sullyjason/interactiles/2x2 Interactiles/switch pins.jpg

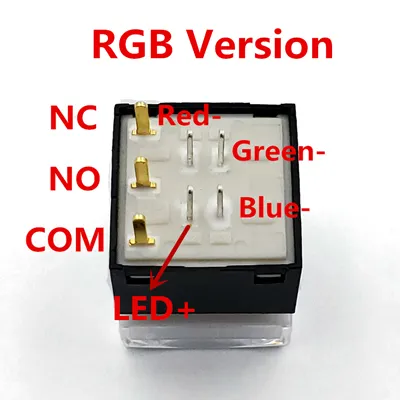
2x2 Interactiles/switch pins.jpg
