sullyjason/interactiles/Interactiles_Controller/Interactiles_Controller.kicad_sch

## KiCad design Interactiles_Controller/Interactiles_Controller.kicad_sch (2026-07-07)

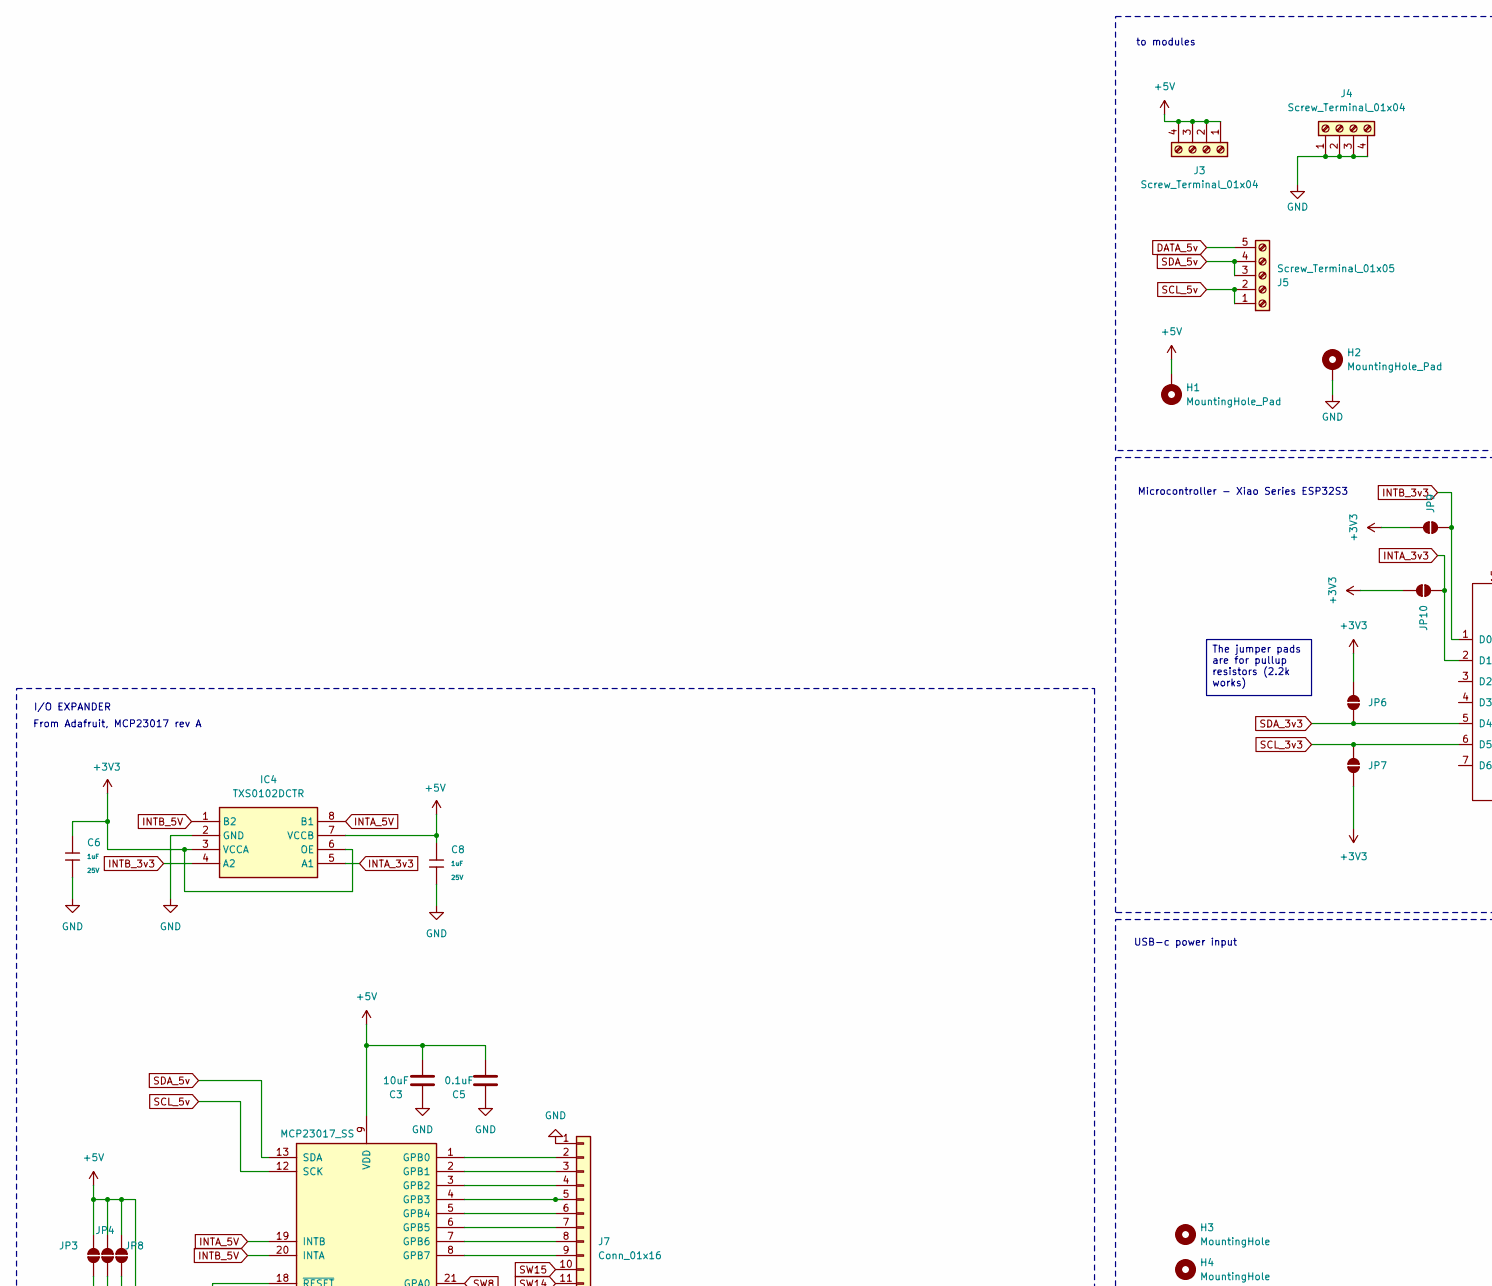
[picture p37: schematic Interactiles_Controller.kicad_sch, part in row 1, column 1]

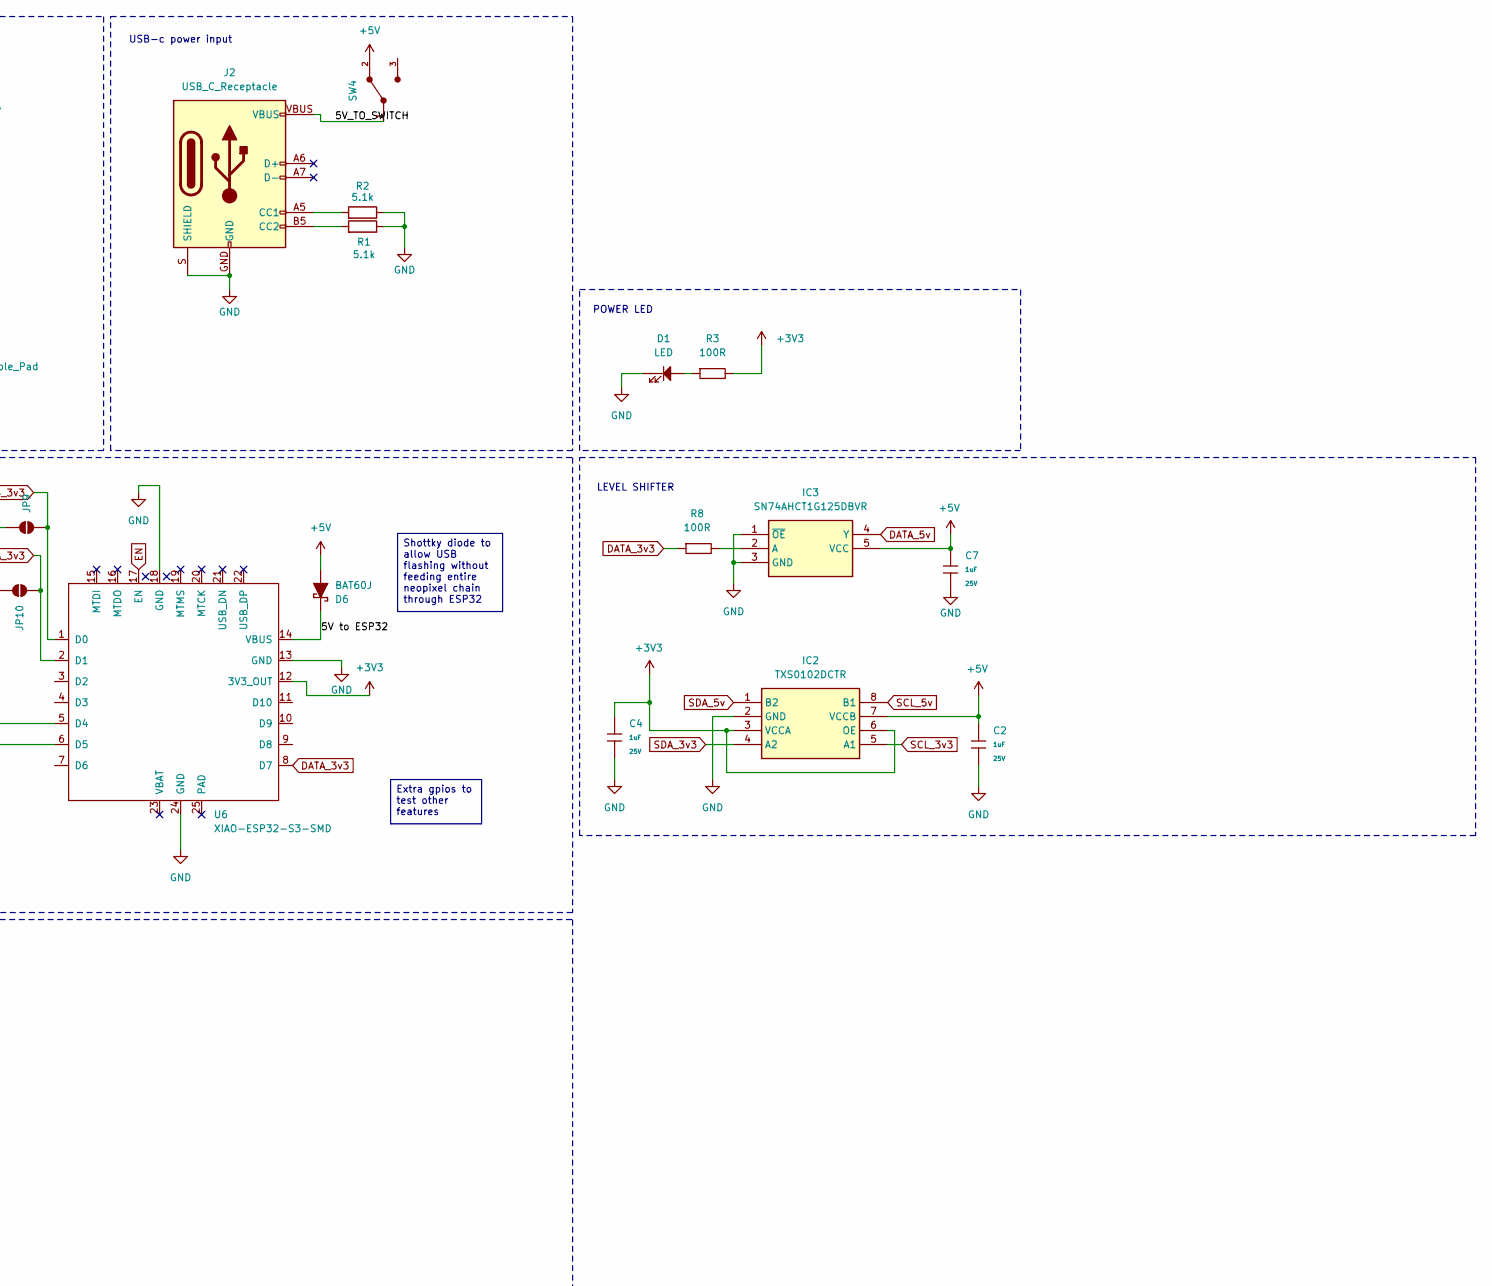
[picture p38: schematic Interactiles_Controller.kicad_sch, part in row 1, column 2]

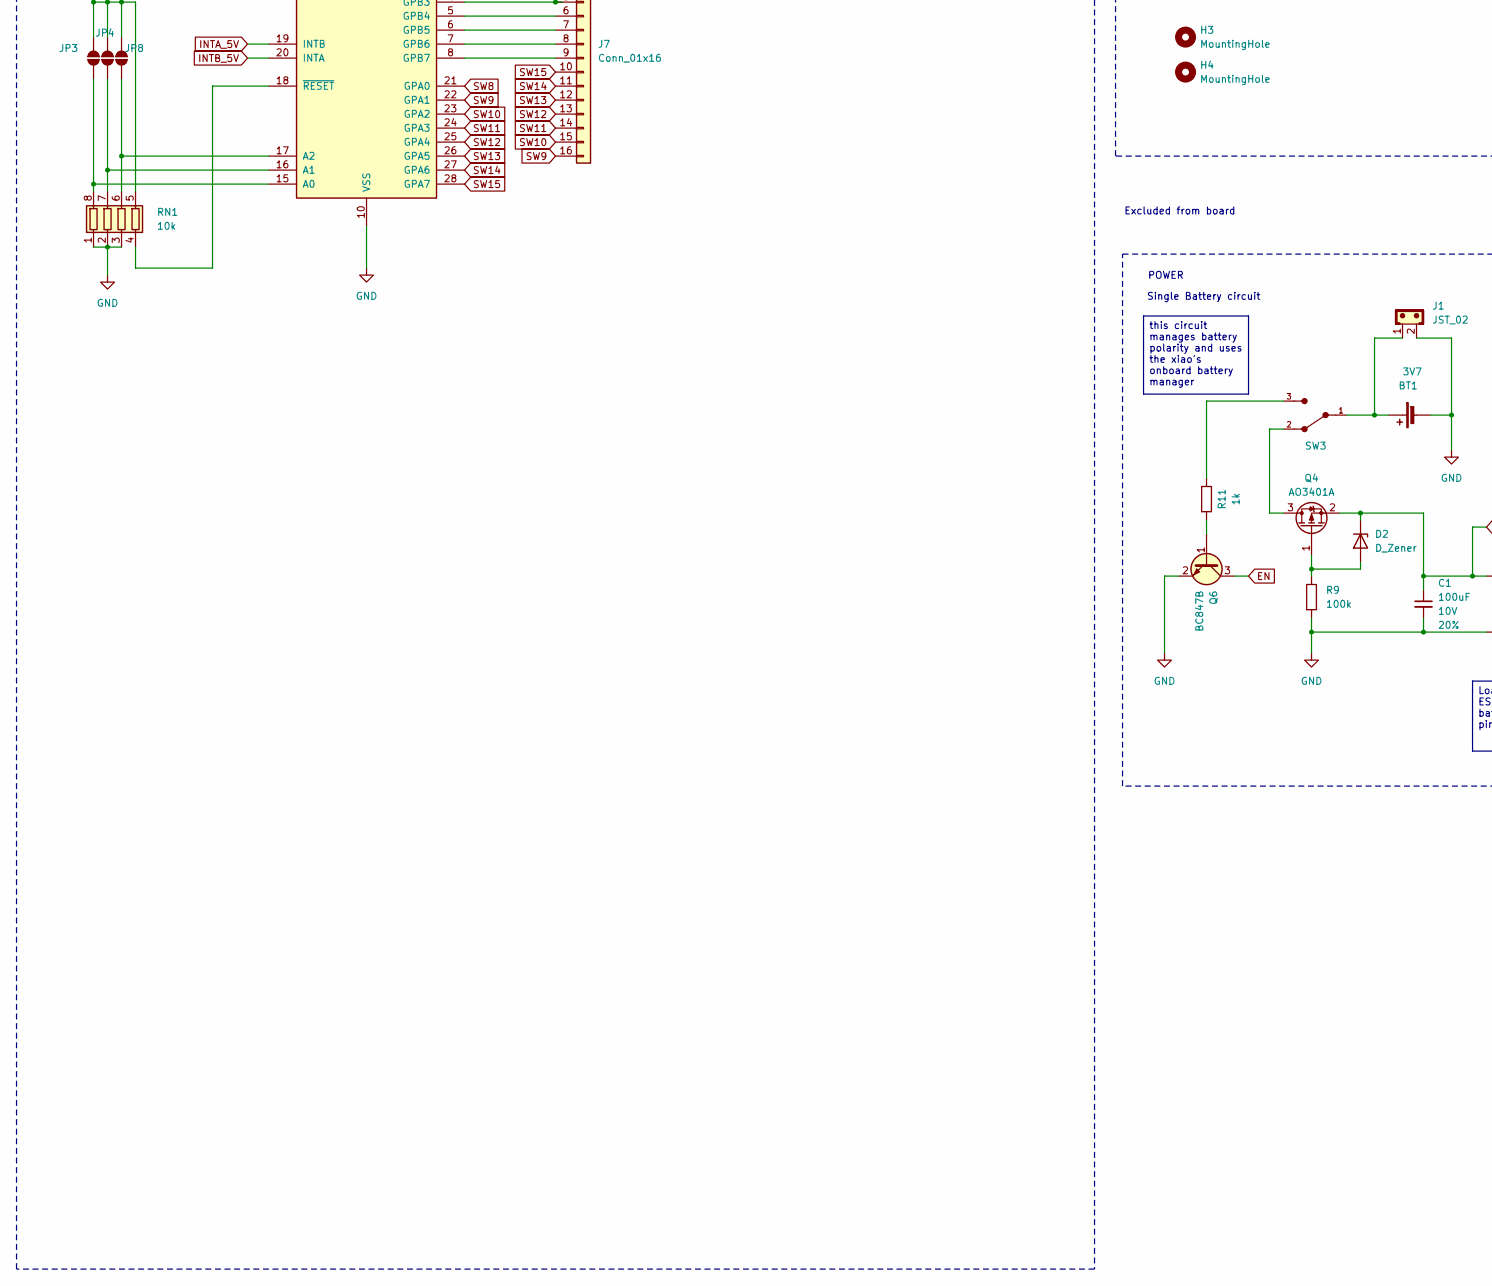
[picture p39: schematic Interactiles_Controller.kicad_sch, part in row 2, column 1]

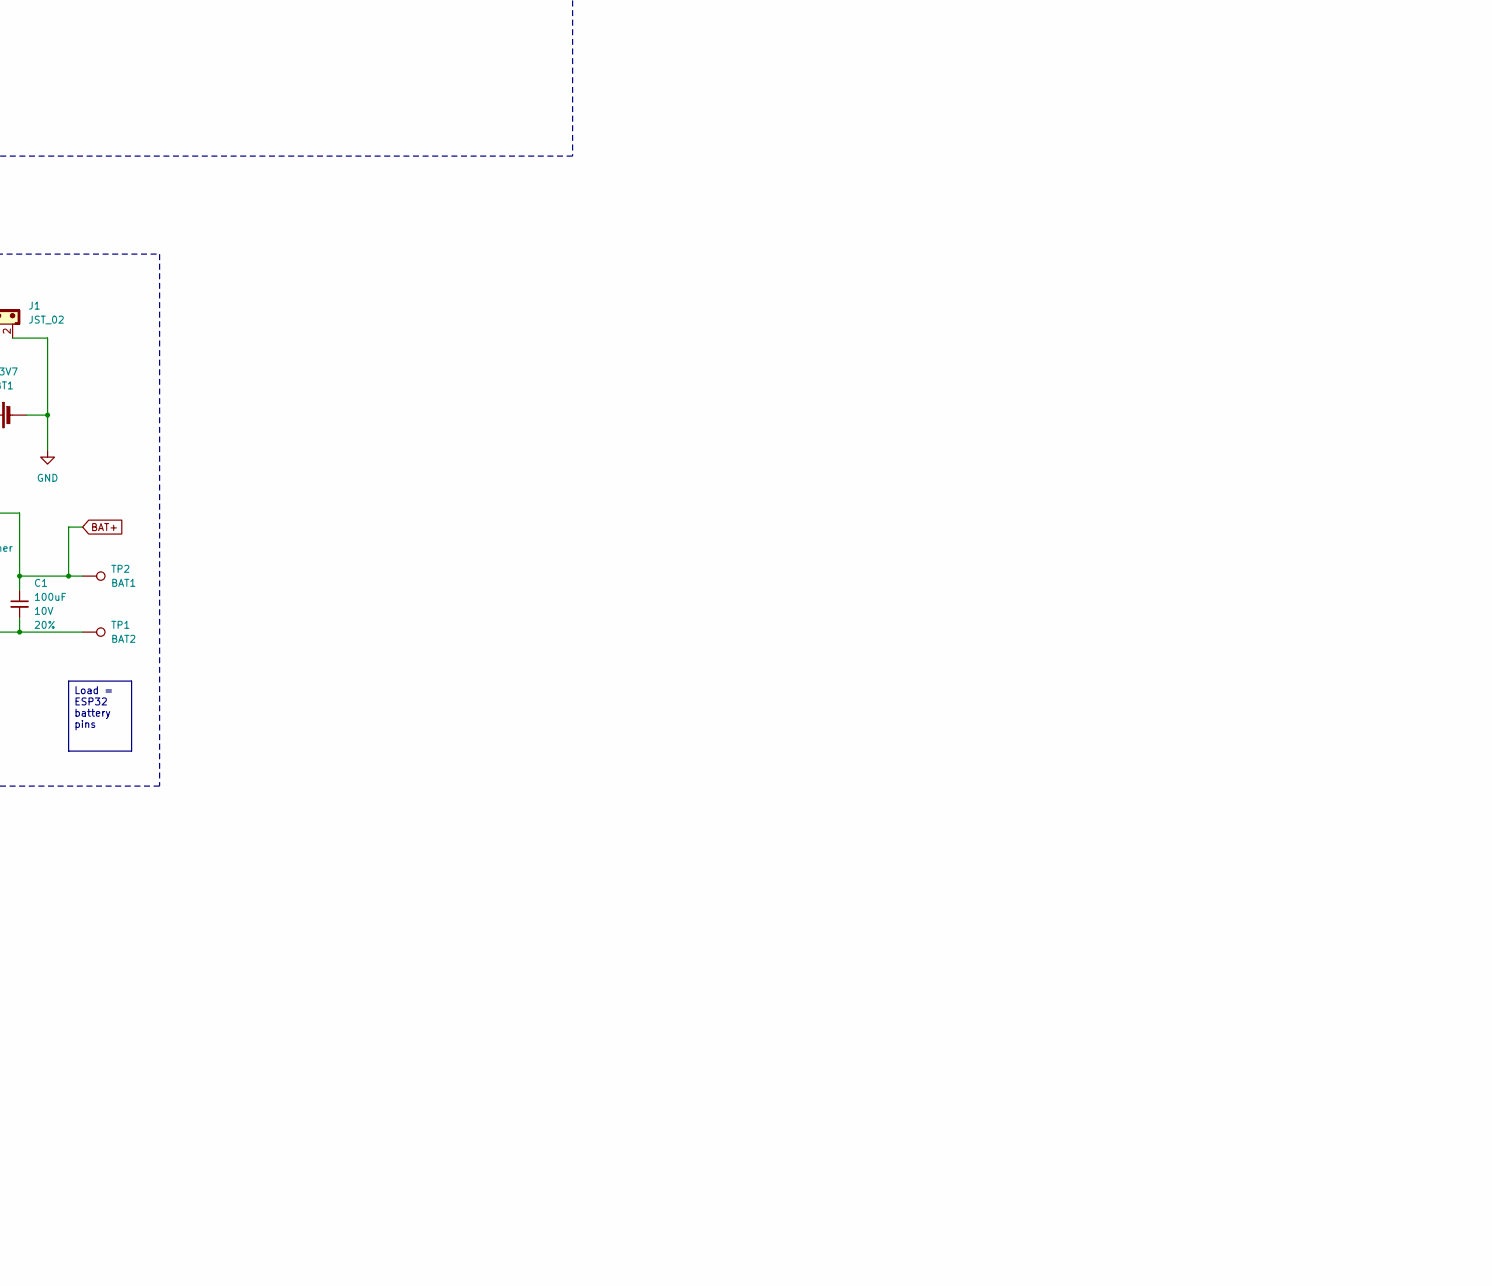
[picture p40: schematic Interactiles_Controller.kicad_sch, part in row 2, column 2]

Parts:
BT1: 3V7; BHC-CR123A
C1: 100uF; C_1206_3216Metric; Voltage 10V; Tolerance 20%
C2, C4, C6, C7, C8: 1uF; C_0402; Voltage Rated 25V; Tolerance ±10%; Part CL05A105KA5NQNC; LCSC C52923
C3: 10uF; C_0603_1608Metric_Pad1.08x0.95mm_HandSolder
C5: 0.1uF; C_0402_1005Metric_Pad0.74x0.62mm_HandSolder
D1: LED; LED_0805_2012Metric_Pad1.15x1.40mm_HandSolder
D2: D_Zener; D_SOD-323_HandSoldering
D6: BAT60J; SOD-323
H1, H2: MountingHole_Pad; MountingHole_3.2mm_M3_Pad_Via
H3, H4: MountingHole; MountingHole_3.2mm_M3_DIN965_Pad_TopBottom
IC2, IC4: TXS0102DCTR; Manufacturer_Part_Number TXS0102DCTR; Mouser Part Number 595-TXS0102DCTR
IC3: SN74AHCT1G125DBVR; Manufacturer_Part_Number SN74AHCT1G125DBVR; Mouser Part Number 595-SNAHCT1G125DBVR
J1: JST_02; JST_PH_S2B-PH-SM4-TB_1x02-1MP_P2.00mm_Horizontal
J2: USB_C_Receptacle; USB-C_16
J3, J4: Screw_Terminal_01x04; Lever_Terminal_1x04_WJ142R-5.08
J5: Screw_Terminal_01x05; Lever_Terminal_1x05_WJ142R-5.08
J7: Conn_01x16; IDC-Header_2x08_P2.54mm_Vertical
JP3, JP4, JP6, JP7, JP8, JP9, JP10: SolderJumper_2_Open; SolderJumper-2_P1.3mm_Open_RoundedPad1.0x1.5mm
Q4: AO3401A; SOT-23
Q6: BC847B; SOT-23
R1, R2: 5.1k; R_0603_1608Metric
R3, R8: 100R; R_0603_1608Metric_Pad0.98x0.95mm_HandSolder
R9: 100k; R_0603_1608Metric
R11: 1k; R_0603_1608Metric_Pad0.98x0.95mm_HandSolder
RN1: 10k; R_Array_Convex_4x0603
SW3: Slide_Switch_SPDT; SW_SPDT_PCM12
SW4: Slide_Switch_SPDT; SW_Slide_SPDT_Straight_CK_OS102011MS2Q
TP1: BAT2; SolderWire-0.1sqmm_1x01_D0.4mm_OD1mm
TP2: BAT1; SolderWire-0.1sqmm_1x01_D0.4mm_OD1mm
U2: MCP23017_SS; SSOP-28_5.3x10.2mm_P0.65mm
U6: XIAO-ESP32-S3-SMD; XIAO-ESP32-S3-DIP

Connections:
5V to ESP32: D6.1 (K), U6.14 (VBUS)
5V_TO_SWITCH: J2.VBUS, SW4.1
+3V3: C4.1, C6.1, IC2.3 (VCCA), IC2.6 (OE), IC4.3 (VCCA), IC4.6 (OE), JP6.2 (B), JP7.1 (A), JP9.2 (B), JP10.1 (A), R3.2, U6.12 (3V3_OUT)
+5V: C2.1, C3.1, C5.1, C7.1, C8.1, D6.2 (A), H1.1, IC2.7 (VCCB), IC3.5 (VCC), IC4.7 (VCCB), J3.1, J3.2, J3.3, J3.4, JP3.2 (B), JP4.2 (B), JP8.2 (B), RN1.5 (R4.2), SW4.2, U2.9 (VDD)
BAT+: C1.1, D2.1 (K), Q4.2 (S), TP2.1
DATA_3v3: R8.1, U6.8 (D7)
DATA_5v: IC3.4 (Y), J5.5
EN: Q6.3 (C), U6.17 (EN)
GND: BT1.2 (-), C1.2, C2.2, C3.2, C4.2, C5.2, C6.2, C7.2, C8.2, D1.1, H2.1, IC2.2 (GND), IC3.1 (~OE), IC3.3 (GND), IC4.2 (GND), J1.2, J2.GND, J2.S (SHIELD), J4.1, J4.2, J4.3, J4.4, J7.1, Q6.2 (E), R1.2, R2.2, R9.1, RN1.1 (R1.1), RN1.2 (R2.1), RN1.3 (R3.1), TP1.1, U2.10 (VSS), U6.13 (GND), U6.18 (GND), U6.24 (GND)
INTA_3v3: IC4.5 (A1), JP10.2 (B), U6.2 (D1)
INTA_5V: IC4.8 (B1), U2.19 (INTB)
INTB_3v3: IC4.4 (A2), JP9.1 (A), U6.1 (D0)
INTB_5V: IC4.1 (B2), U2.20 (INTA)
unnamed: BT1.1 (+), J1.1, SW3.1
unnamed: D1.2, R3.1
unnamed: D2.2 (A), Q4.1 (G), R9.2
unnamed: IC3.2 (A), R8.2
unnamed: J2.A5 (CC1), R1.1
unnamed: J2.A6 (D+), J2.B6 (D+)
unnamed: J2.A7 (D-), J2.B7 (D-)
unnamed: J2.B5 (CC2), R2.1
unnamed: J7.2, U2.1 (GPB0)
unnamed: J7.3, U2.2 (GPB1)
unnamed: J7.4, U2.3 (GPB2)
unnamed: J7.5, U2.4 (GPB3)
unnamed: J7.6, U2.5 (GPB4)
unnamed: J7.7, U2.6 (GPB5)
unnamed: J7.8, U2.7 (GPB6)
unnamed: J7.9, U2.8 (GPB7)
unnamed: JP3.1 (A), RN1.8 (R1.2), U2.15 (A0)
unnamed: JP4.1 (A), RN1.7 (R2.2), U2.16 (A1)
unnamed: JP8.1 (A), RN1.6 (R3.2), U2.17 (A2)
unnamed: Q4.3 (D), SW3.2
unnamed: Q6.1 (B), R11.1
unnamed: R11.2, SW3.3
unnamed: RN1.4 (R4.1), U2.18 (~RESET)
SCL_3v3: IC2.5 (A1), JP7.2 (B), U6.6 (D5)
SCL_5v: IC2.8 (B1), J5.1, J5.2, U2.12 (SCK)
SDA_3v3: IC2.4 (A2), JP6.1 (A), U6.5 (D4)
SDA_5v: IC2.1 (B2), J5.3, J5.4, U2.13 (SDA)
SW8: U2.21 (GPA0)
SW9: J7.16, U2.22 (GPA1)
SW10: J7.15, U2.23 (GPA2)
SW11: J7.14, U2.24 (GPA3)
SW12: J7.13, U2.25 (GPA4)
SW13: J7.12, U2.26 (GPA5)
SW14: J7.11, U2.27 (GPA6)
SW15: J7.10, U2.28 (GPA7)

Notes on the sheet:
Single Battery circuit
Excluded from board
Microcontroller - Xiao Series ESP32S3
USB-c power input
LEVEL SHIFTER
POWER LED
POWER
I/O EXPANDER
to modules
From Adafruit, MCP23017 rev A
Extra gpios to test other features
The jumper pads are for pullup resistors (2.2k works)
Load = ESP32 battery pins
Shottky diode to allow USB flashing without feeding entire neopixel chain through ESP32
this circuit manages battery polarity and uses the xiao's onboard battery manager
