sullyjason/interactiles/2x2 Interactiles/PCB/Controller PCB/RGB 2x2 with WS2811.kicad_sch

## KiCad design 2x2 Interactiles/PCB/Controller PCB/RGB 2x2 with WS2811.kicad_sch (2024-11-05)

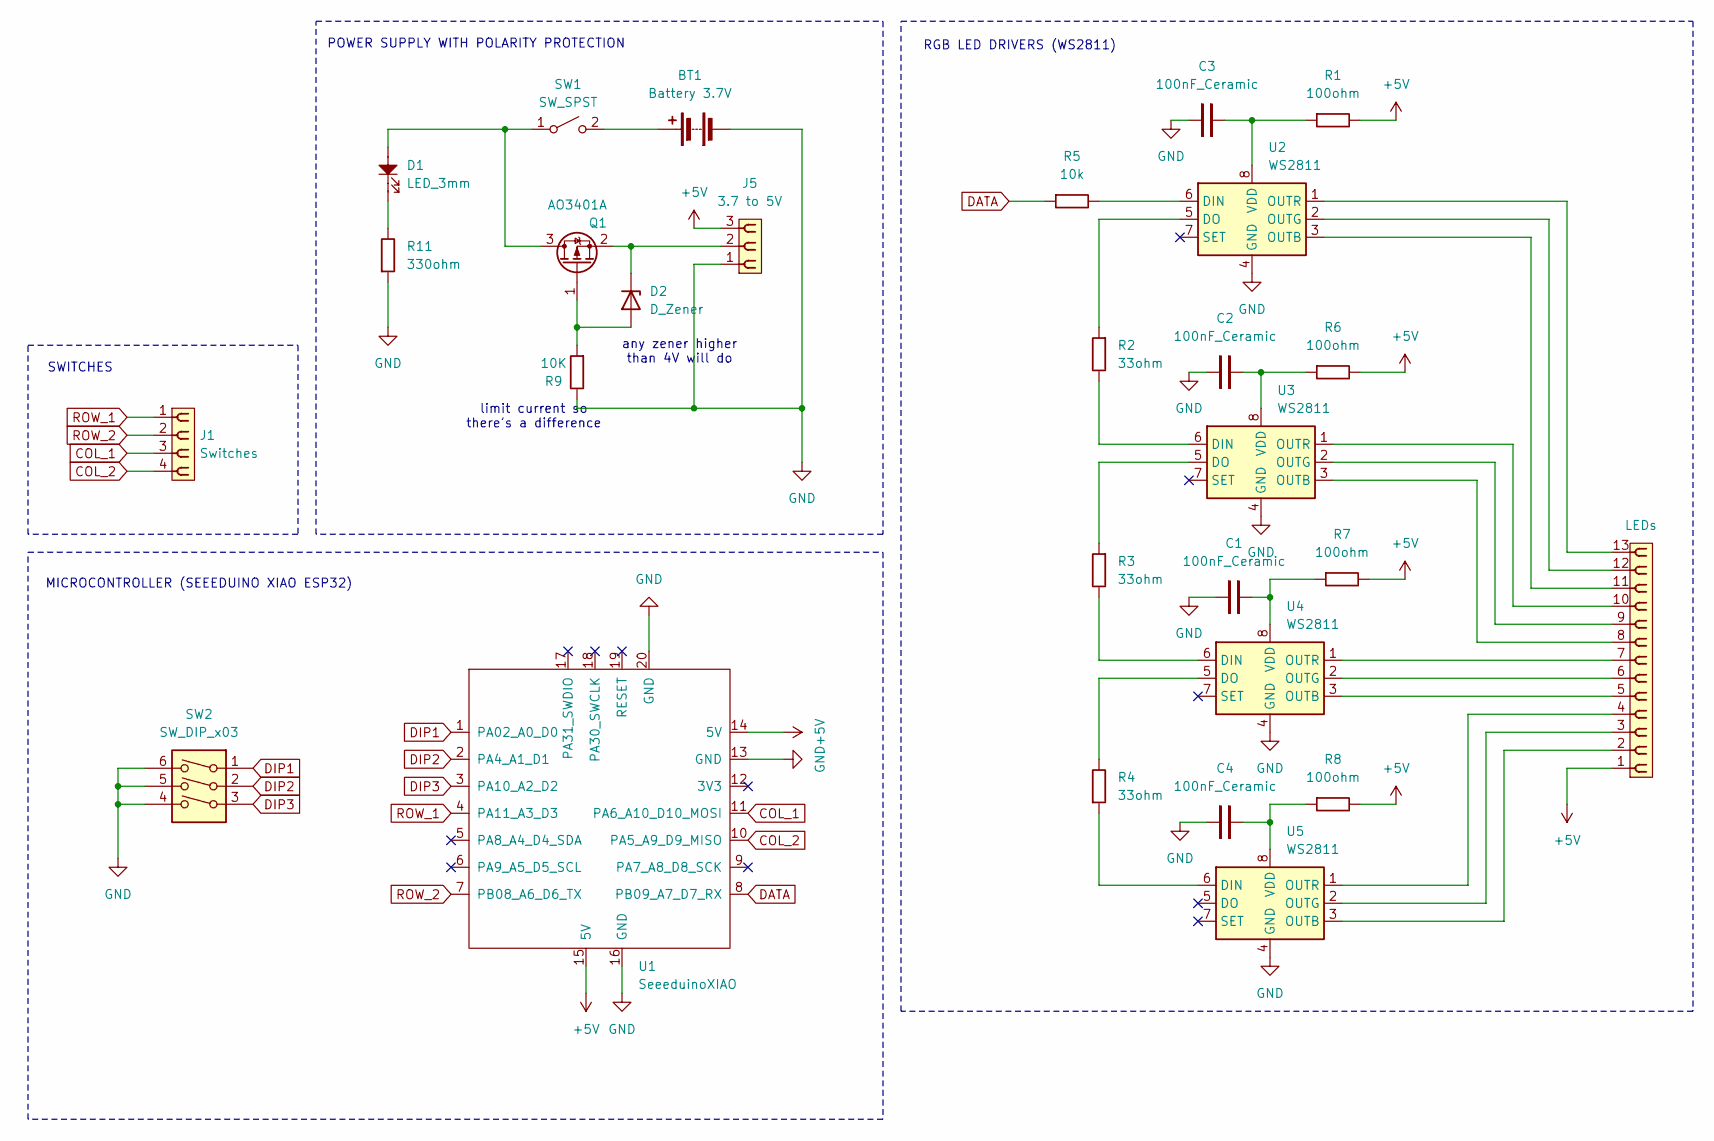
[picture p41: schematic RGB 2x2 with WS2811.kicad_sch]

Parts:
BT1: Battery 3.7V; BHC-CR123A
C1, C2, C3, C4: 100nF_Ceramic; C_0805_2012Metric_Pad1.18x1.45mm_HandSolder
D1: LED_3mm; LED_D3.0mm
D2: D_Zener
J1: Switches; PinSocket_1x04_P2.54mm_Vertical
J2: LEDs; PinSocket_1x13_P2.54mm_Vertical
J5: 3.7 to 5V; PinSocket_1x03_P2.54mm_Vertical
Q1: AO3401A; SOT-23
R1, R6, R7, R8: 100ohm; R_0805_2012Metric_Pad1.20x1.40mm_HandSolder
R2, R3, R4: 33ohm; R_0805_2012Metric_Pad1.20x1.40mm_HandSolder
R5: 10k; R_0805_2012Metric_Pad1.20x1.40mm_HandSolder
R9: 10K; R_0805_2012Metric_Pad1.20x1.40mm_HandSolder
R11: 330ohm; R_0805_2012Metric_Pad1.20x1.40mm_HandSolder
SW1: SW_SPST; SW_Slide_SPDT_Angled_CK_OS102011MA1Q
SW2: SW_DIP_x03; SW_DIP_SPSTx03_Slide_9.78x9.8mm_W7.62mm_P2.54mm
U1: SeeeduinoXIAO; Seeeduino XIAO-MOUDLE14P-2.54-21X17.8MM
U2, U3, U4, U5: WS2811; HSOP-8-1EP_3.9x4.9mm_P1.27mm_EP2.3x2.3mm

Connections:
+5V: J2.1, J5.3, R1.2, R6.2, R7.2, R8.2, U1.14 (5V), U1.15 (5V)
COL_1: J1.3, U1.11 (PA6_A10_D10_MOSI)
COL_2: J1.4, U1.10 (PA5_A9_D9_MISO)
DATA: R5.1, U1.8 (PB09_A7_D7_RX)
DIP1: SW2.1, U1.1 (PA02_A0_D0)
DIP2: SW2.2, U1.2 (PA4_A1_D1)
DIP3: SW2.3, U1.3 (PA10_A2_D2)
GND: BT1.2 (-), C1.1, C2.1, C3.1, C4.1, J5.1, R9.2, R11.1, SW2.4, SW2.5, SW2.6, U1.13 (GND), U1.16 (GND), U1.20 (GND), U2.4 (GND), U3.4 (GND), U4.4 (GND), U5.4 (GND)
unnamed: BT1.1 (+), SW1.2 (B)
unnamed: C1.2, R7.1, U4.8 (VDD)
unnamed: C2.2, R6.1, U3.8 (VDD)
unnamed: C3.2, R1.1, U2.8 (VDD)
unnamed: C4.2, R8.1, U5.8 (VDD)
unnamed: D1.1, R11.2
unnamed: D1.2, Q1.3 (D), SW1.1 (A)
unnamed: D2.1 (K), J5.2, Q1.2 (S)
unnamed: D2.2 (A), Q1.1 (G), R9.1
unnamed: J2.2, U5.3 (OUTB)
unnamed: J2.3, U5.2 (OUTG)
unnamed: J2.4, U5.1 (OUTR)
unnamed: J2.5, U4.3 (OUTB)
unnamed: J2.6, U4.2 (OUTG)
unnamed: J2.7, U4.1 (OUTR)
unnamed: J2.8, U3.3 (OUTB)
unnamed: J2.9, U3.2 (OUTG)
unnamed: J2.10, U3.1 (OUTR)
unnamed: J2.11, U2.3 (OUTB)
unnamed: J2.12, U2.2 (OUTG)
unnamed: J2.13, U2.1 (OUTR)
unnamed: R2.1, U2.5 (DO)
unnamed: R2.2, U3.6 (DIN)
unnamed: R3.1, U3.5 (DO)
unnamed: R3.2, U4.6 (DIN)
unnamed: R4.1, U5.6 (DIN)
unnamed: R4.2, U4.5 (DO)
unnamed: R5.2, U2.6 (DIN)
ROW_1: J1.1, U1.4 (PA11_A3_D3)
ROW_2: J1.2, U1.7 (PB08_A6_D6_TX)

Notes on the sheet:
any zener higher than 4V will do
limit current so there's a difference
SWITCHES
POWER SUPPLY WITH POLARITY PROTECTION
RGB LED DRIVERS (WS2811)
MICROCONTROLLER (SEEEDUINO XIAO ESP32)
