sullyjason/interactiles/2x2 Interactiles/PCB/Switches PCB/Honyone RGB Shield.kicad_sch

## KiCad design 2x2 Interactiles/PCB/Switches PCB/Honyone RGB Shield.kicad_sch (2024-11-05)

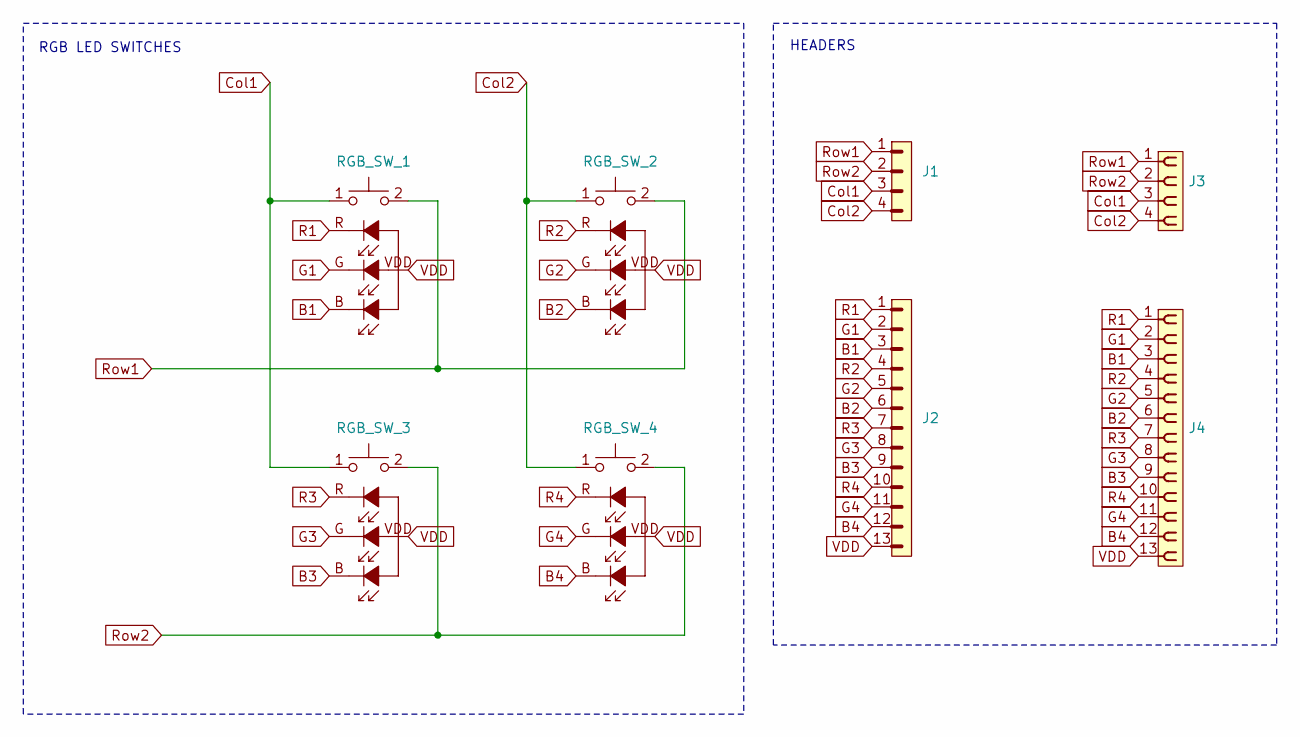
[picture p42: schematic Honyone RGB Shield.kicad_sch]

Parts:
J1: PINHD_1x4_Male; PinHeader_1x04_P2.54mm_Vertical
J2: PINHD_1x13_Male; PinHeader_1x13_P2.54mm_Vertical
J3: PINHD_1x4_Male; PinSocket_1x04_P2.54mm_Vertical
J4: PINHD_1x13_Female; PinSocket_1x13_P2.54mm_Vertical
SW1: RGB_SW_1; Honyone Tactile Switch RGB
SW2: RGB_SW_2; Honyone Tactile Switch RGB
SW3: RGB_SW_3; Honyone Tactile Switch RGB
SW4: RGB_SW_4; Honyone Tactile Switch RGB

Connections:
B1: J2.3, J4.3, SW1.B
B2: J2.6, J4.6, SW2.B
B3: J2.9, J4.9, SW3.B
B4: J2.12, J4.12, SW4.B
Col1: J1.3, J3.3, SW1.1, SW3.1
Col2: J1.4, J3.4, SW2.1, SW4.1
G1: J2.2, J4.2, SW1.G
G2: J2.5, J4.5, SW2.G
G3: J2.8, J4.8, SW3.G
G4: J2.11, J4.11, SW4.G
R1: J2.1, J4.1, SW1.R
R2: J2.4, J4.4, SW2.R
R3: J2.7, J4.7, SW3.R
R4: J2.10, J4.10, SW4.R
Row1: J1.1, J3.1, SW1.2, SW2.2
Row2: J1.2, J3.2, SW3.2, SW4.2
VDD: J2.13, J4.13, SW1.VDD, SW2.VDD, SW3.VDD, SW4.VDD

Notes on the sheet:
HEADERS
RGB LED SWITCHES
