sullyjason/interactiles/Button_Modules/Large/Module_Large/Interactiles_Module_Neopixel.kicad_sch

## KiCad design Button_Modules/Large/Module_Large/Interactiles_Module_Neopixel.kicad_sch (2024-11-05)

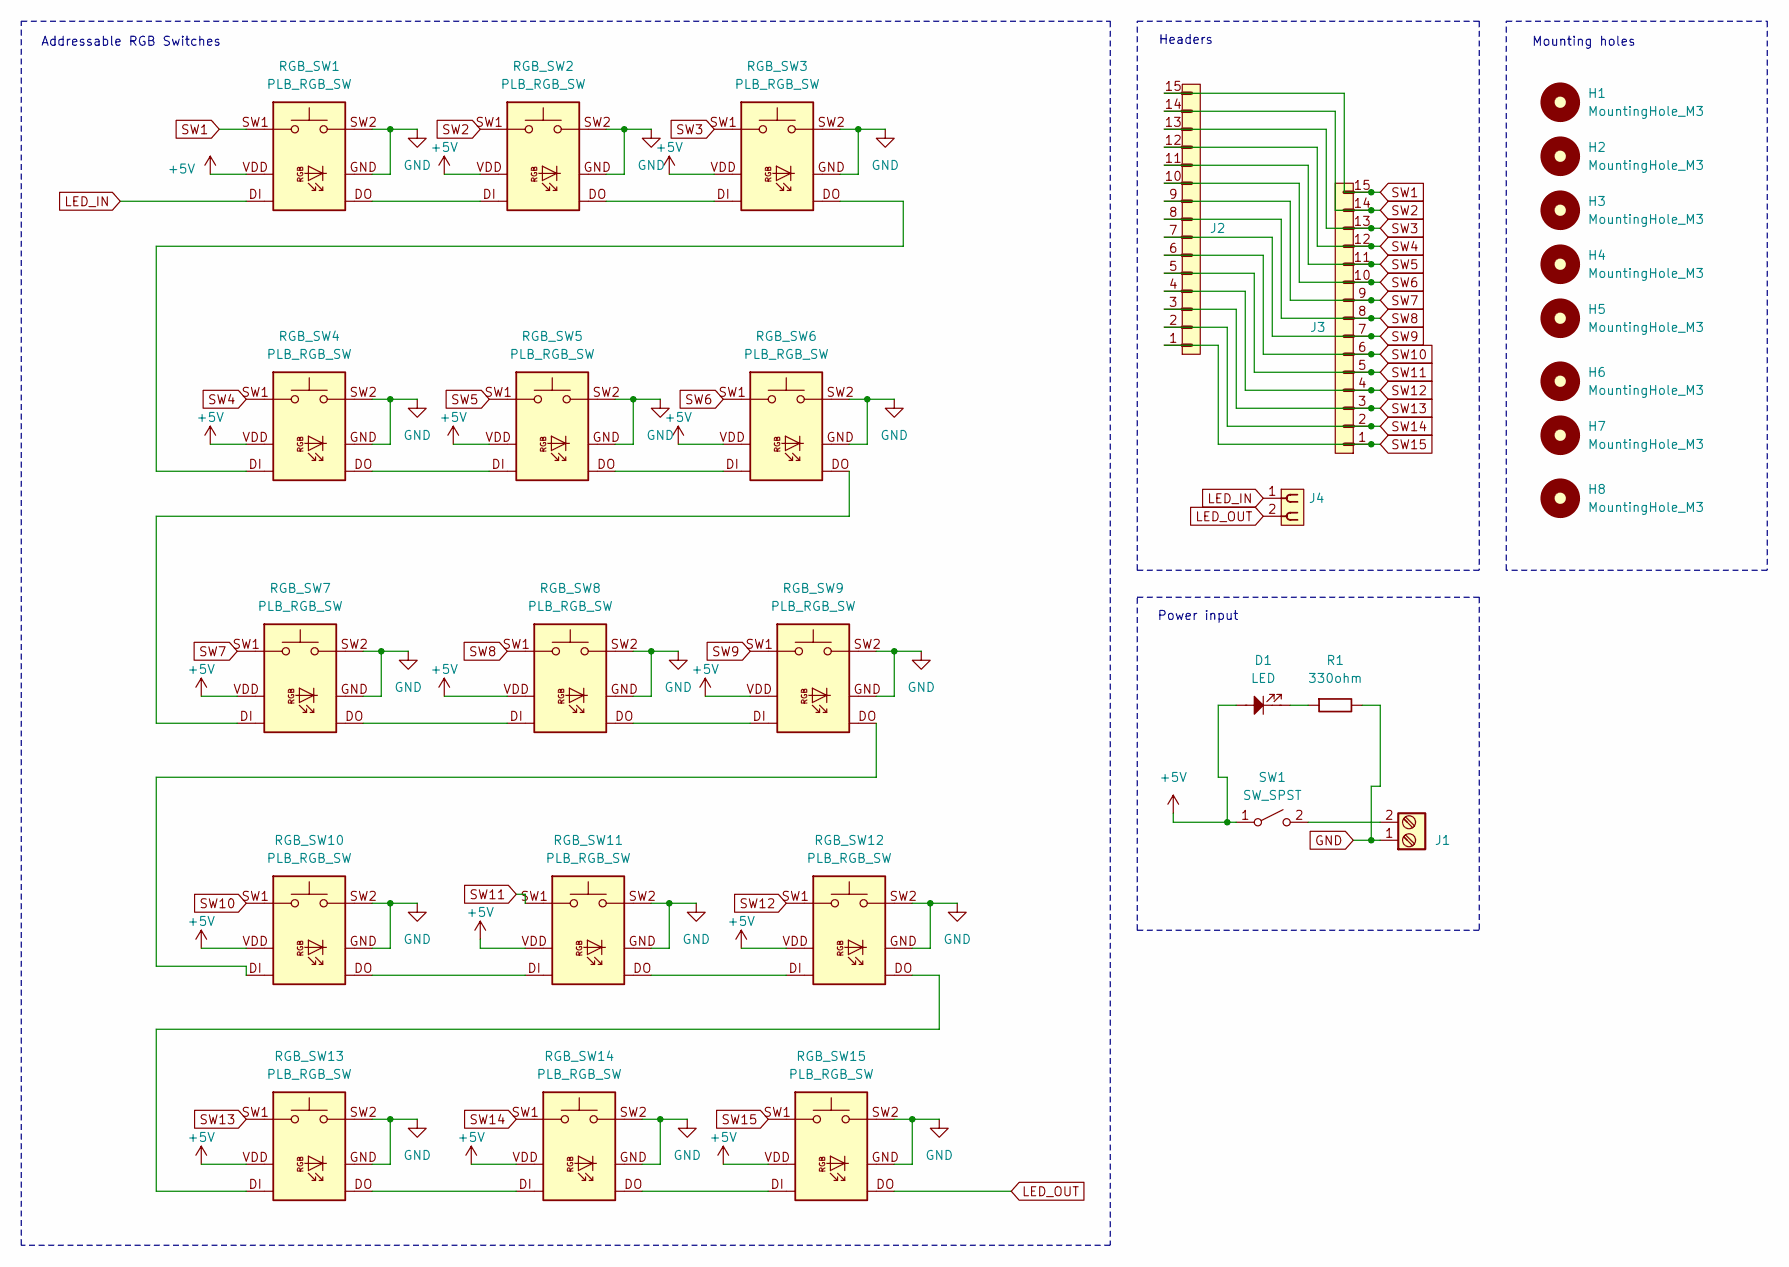
[picture p43: schematic Interactiles_Module_Neopixel.kicad_sch]

Parts:
D1: LED; LED_1206_3216Metric_Pad1.42x1.75mm_HandSolder
H1, H2, H3, H4, H5, H6, H7, H8: MountingHole_M3; MountingHole_3.2mm_M3_DIN965_Pad
J1: Screw_Terminal_2_P3.50mm; TerminalBlock_Phoenix_PT-1,5-2-3.5-H_1x02_P3.50mm_Horizontal
J2: PINHD_1x15_Male; PinHeader_1x15_P2.54mm_Vertical
J3: PINHD_1x15_Male; TE_1-84952-6_1x16-1MP_P1.0mm_Horizontal
J4: PINHD_1x2_Female; PinSocket_1x02_P2.54mm_Vertical
R1: 330ohm; R_0805_2012Metric_Pad1.20x1.40mm_HandSolder
RGB_SW1, RGB_SW2, RGB_SW3, RGB_SW4, RGB_SW5, RGB_SW6, RGB_SW7, RGB_SW8, RGB_SW9, RGB_SW10, RGB_SW11, RGB_SW12, RGB_SW13, RGB_SW14, RGB_SW15: PLB_RGB_SW; PLB-N1PRGB-GTW-AI
SW1: SW_SPST; SW_DPDT_CK_JS202011JCQN

Connections:
+5V: D1.2, RGB_SW1.VDD, RGB_SW2.VDD, RGB_SW3.VDD, RGB_SW4.VDD, RGB_SW5.VDD, RGB_SW6.VDD, RGB_SW7.VDD, RGB_SW8.VDD, RGB_SW9.VDD, RGB_SW10.VDD, RGB_SW11.VDD, RGB_SW12.VDD, RGB_SW13.VDD, RGB_SW14.VDD, RGB_SW15.VDD, SW1.1 (A)
GND: J1.1, R1.2, RGB_SW1.GND, RGB_SW1.SW2, RGB_SW2.GND, RGB_SW2.SW2, RGB_SW3.GND, RGB_SW3.SW2, RGB_SW4.GND, RGB_SW4.SW2, RGB_SW5.GND, RGB_SW5.SW2, RGB_SW6.GND, RGB_SW6.SW2, RGB_SW7.GND, RGB_SW7.SW2, RGB_SW8.GND, RGB_SW8.SW2, RGB_SW9.GND, RGB_SW9.SW2, RGB_SW10.GND, RGB_SW10.SW2, RGB_SW11.GND, RGB_SW11.SW2, RGB_SW12.GND, RGB_SW12.SW2, RGB_SW13.GND, RGB_SW13.SW2, RGB_SW14.GND, RGB_SW14.SW2, RGB_SW15.GND, RGB_SW15.SW2
LED_IN: J4.1, RGB_SW1.DI (DIN)
LED_OUT: J4.2, RGB_SW15.DO
unnamed: D1.1, R1.1
unnamed: J1.2, SW1.2 (B)
unnamed: RGB_SW1.DO, RGB_SW2.DI (DIN)
unnamed: RGB_SW2.DO, RGB_SW3.DI (DIN)
unnamed: RGB_SW3.DO, RGB_SW4.DI (DIN)
unnamed: RGB_SW4.DO, RGB_SW5.DI (DIN)
unnamed: RGB_SW5.DO, RGB_SW6.DI (DIN)
unnamed: RGB_SW6.DO, RGB_SW7.DI (DIN)
unnamed: RGB_SW7.DO, RGB_SW8.DI (DIN)
unnamed: RGB_SW8.DO, RGB_SW9.DI (DIN)
unnamed: RGB_SW9.DO, RGB_SW10.DI (DIN)
unnamed: RGB_SW10.DO, RGB_SW11.DI (DIN)
unnamed: RGB_SW11.DO, RGB_SW12.DI (DIN)
unnamed: RGB_SW12.DO, RGB_SW13.DI (DIN)
unnamed: RGB_SW13.DO, RGB_SW14.DI (DIN)
unnamed: RGB_SW14.DO, RGB_SW15.DI (DIN)
SW1: J2.15, J3.15, RGB_SW1.SW1
SW2: J2.14, J3.14, RGB_SW2.SW1
SW3: J2.13, J3.13, RGB_SW3.SW1
SW4: J2.12, J3.12, RGB_SW4.SW1
SW5: J2.11, J3.11, RGB_SW5.SW1
SW6: J2.10, J3.10, RGB_SW6.SW1
SW7: J2.9, J3.9, RGB_SW7.SW1
SW8: J2.8, J3.8, RGB_SW8.SW1
SW9: J2.7, J3.7, RGB_SW9.SW1
SW10: J2.6, J3.6, RGB_SW10.SW1
SW11: J2.5, J3.5, RGB_SW11.SW1
SW12: J2.4, J3.4, RGB_SW12.SW1
SW13: J2.3, J3.3, RGB_SW13.SW1
SW14: J2.2, J3.2, RGB_SW14.SW1
SW15: J2.1, J3.1, RGB_SW15.SW1

Notes on the sheet:
Headers
Addressable RGB Switches
Power input
Mounting holes
