sullyjason/interactiles/Button_Modules/Large/Module_Large_IOexpander/Module_Large_IOexpander.kicad_sch

## KiCad design Button_Modules/Large/Module_Large_IOexpander/Module_Large_IOexpander.kicad_sch (2026-07-07)

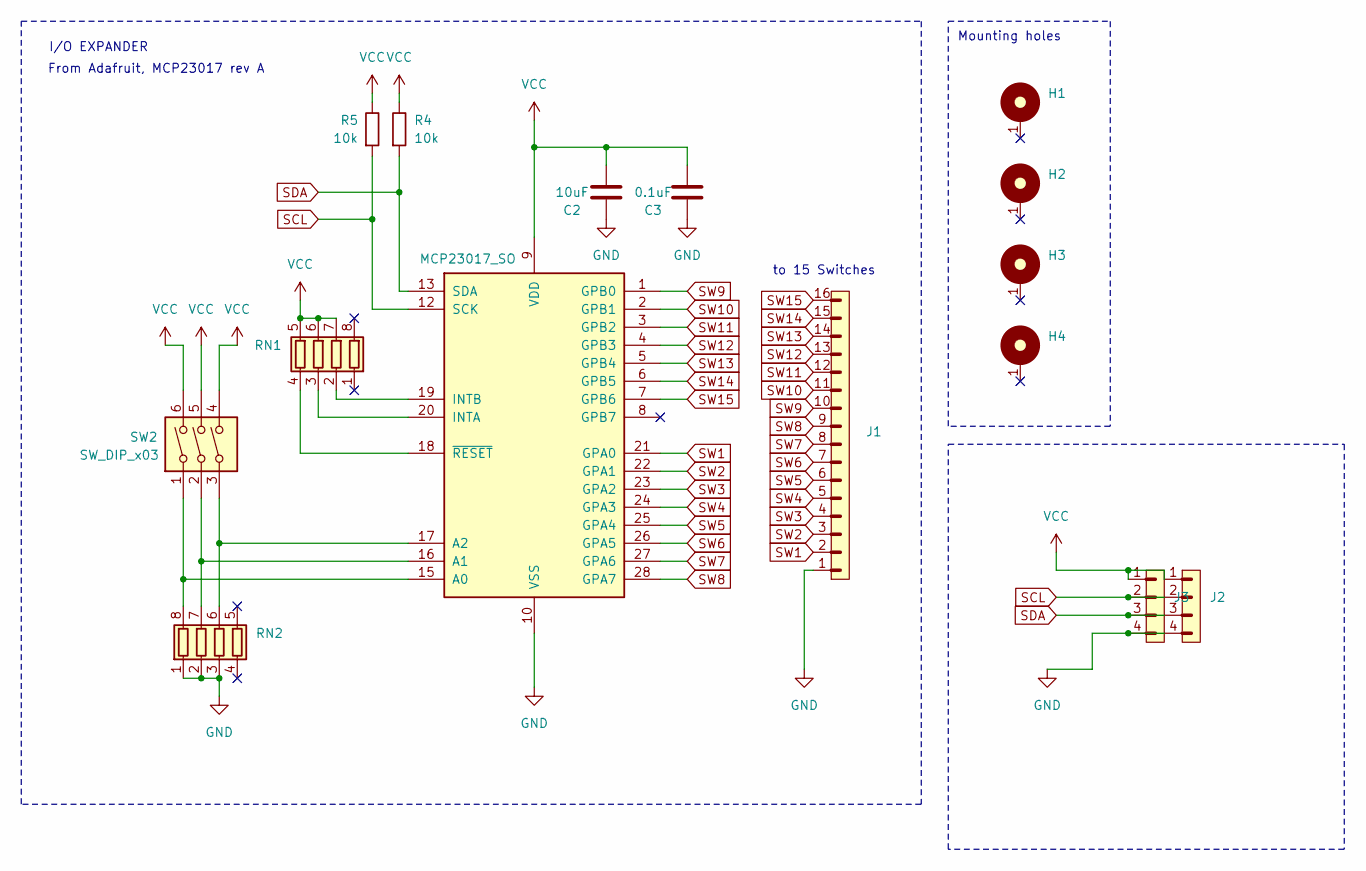
[picture p44: schematic Module_Large_IOexpander.kicad_sch]

Parts:
C2: 10uF; C_0805_2012Metric_Pad1.18x1.45mm_HandSolder
C3: 0.1uF; C_0805_2012Metric_Pad1.18x1.45mm_HandSolder
H1, H2, H3, H4: MountingHole_M3_3.2mm_Pad; MountingHole_3.2mm_Pad
J1: PINHD_1x16_Male; TE_1-84952-6_1x16-1MP_P1.0mm_Horizontal
J2: PINHD_1x4_Male; Molex_PicoBlade_53261-0471_1x04-1MP_P1.25mm_Horizontal
J3: PINHD_1x4_Male; PinHeader_1x04_P2.54mm_Vertical
R4, R5: 10k; C_0805_2012Metric_Pad1.18x1.45mm_HandSolder
RN1, RN2: R_Pack04; R_Array_Concave_4x0603
SW2: SW_DIP_x03; SW_DIP_SPSTx03_Slide_6.7x9.18mm_W8.61mm_P2.54mm_LowProfile
U3: MCP23017_SO; SOIC-28W_7.5x17.9mm_P1.27mm

Connections:
GND: C2.2, C3.2, J1.1, J2.4, J3.4, RN2.1 (R1.1), RN2.2 (R2.1), RN2.3 (R3.1), U3.10 (VSS)
unnamed: RN1.2 (R2.1), U3.19 (INTB)
unnamed: RN1.3 (R3.1), U3.20 (INTA)
unnamed: RN1.4 (R4.1), U3.18 (~RESET)
unnamed: RN2.6 (R3.2), SW2.3, U3.17 (A2)
unnamed: RN2.7 (R2.2), SW2.2, U3.16 (A1)
unnamed: RN2.8 (R1.2), SW2.1, U3.15 (A0)
SCL: J2.2, J3.2, R5.1, U3.12 (SCK)
SDA: J2.3, J3.3, R4.1, U3.13 (SDA)
SW1: J1.2, U3.21 (GPA0)
SW2: J1.3, U3.22 (GPA1)
SW3: J1.4, U3.23 (GPA2)
SW4: J1.5, U3.24 (GPA3)
SW5: J1.6, U3.25 (GPA4)
SW6: J1.7, U3.26 (GPA5)
SW7: J1.8, U3.27 (GPA6)
SW8: J1.9, U3.28 (GPA7)
SW9: J1.10, U3.1 (GPB0)
SW10: J1.11, U3.2 (GPB1)
SW11: J1.12, U3.3 (GPB2)
SW12: J1.13, U3.4 (GPB3)
SW13: J1.14, U3.5 (GPB4)
SW14: J1.15, U3.6 (GPB5)
SW15: J1.16, U3.7 (GPB6)
VCC: C2.1, C3.1, J2.1, J3.1, R4.2, R5.2, RN1.5 (R4.2), RN1.6 (R3.2), RN1.7 (R2.2), SW2.4, SW2.5, SW2.6, U3.9 (VDD)

Notes on the sheet:
to 15 Switches
I/O EXPANDER
From Adafruit, MCP23017 rev A
Mounting holes
